FPGA-Computer/STM8-Gyrostick/software/USB HID firmware/USB + I2C waveform.png

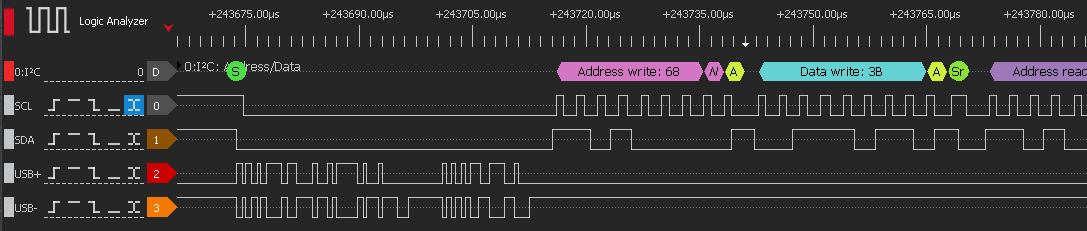
software/USB HID firmware/USB + I2C waveform.png
